kdsparks/data-efficient-satellite/gps/Example3_GetPosition/Example3_GetPosition.ino

/*
  Reading lat and long via UBX binary commands - no more NMEA parsing!
  By: Nathan Seidle
  SparkFun Electronics
  Date: January 3rd, 2019
  License: MIT. See license file for more information but you can
  basically do whatever you want with this code.

  This example shows how to query a u-blox module for its lat/long/altitude. We also
  turn off the NMEA output on the I2C port. This decreases the amount of I2C traffic 
  dramatically.

  Note: Long/lat are large numbers because they are * 10^7. To convert lat/long
  to something google maps understands simply divide the numbers by 10,000,000. We 
  do this so that we don't have to use floating point numbers.

  Leave NMEA parsing behind. Now you can simply ask the module for the datums you want!

  Feel like supporting open source hardware?
  Buy a board from SparkFun!
  ZED-F9P RTK2: https://www.sparkfun.com/products/15136
  NEO-M8P RTK: https://www.sparkfun.com/products/15005
  SAM-M8Q: https://www.sparkfun.com/products/15106

  Hardware Connections:
  Plug a Qwiic cable into the GNSS and a BlackBoard
  If you don't have a platform with a Qwiic connection use the SparkFun Qwiic Breadboard Jumper (https://www.sparkfun.com/products/14425)
  Open the serial monitor at 115200 baud to see the output
*/

#include <Wire.h> //Needed for I2C to GNSS

#include <SparkFun_u-blox_GNSS_Arduino_Library.h> //http://librarymanager/All#SparkFun_u-blox_GNSS
SFE_UBLOX_GNSS myGNSS;

long lastTime = 0; //Simple local timer. Limits amount if I2C traffic to u-blox module.

void setup()
{
  Serial.begin(115200);
  while (!Serial); //Wait for user to open terminal
  Serial.println("SparkFun u-blox Example");

  Wire1.begin();

  //myGNSS.enableDebugging(); // Uncomment this line to enable helpful debug messages on Serial

  if (myGNSS.begin(Wire1) == false) //Connect to the u-blox module using Wire port
  {
    Serial.println(F("u-blox GNSS not detected at default I2C address. Please check wiring. Freezing."));
    while (1);
  }

  myGNSS.setI2COutput(COM_TYPE_UBX); //Set the I2C port to output UBX only (turn off NMEA noise)
  myGNSS.saveConfigSelective(VAL_CFG_SUBSEC_IOPORT); //Save (only) the communications port settings to flash and BBR
}

void loop()
{
  //Query module only every second. Doing it more often will just cause I2C traffic.
  //The module only responds when a new position is available
  if (millis() - lastTime > 1000)
  {
    lastTime = millis(); //Update the timer
    
    long latitude = myGNSS.getLatitude(); // latitude gives raw GPS reading (degrees *10^-7)
    double actualLatitude = (double)latitude / 10000000.0; // divide by 10,000,000 to get lat readable by google maps
    Serial.print(F("Lat: "));
    Serial.print(actualLatitude, 6); // forces display of 6 decimals (or more)

    long longitude = myGNSS.getLongitude(); // longitude gives raw GPS reading (degrees *10^-7)
    double actualLongitude = (double)longitude / 10000000.0; // divide by 10,000,000 to get long readable by google maps
    Serial.print(F(" Long: "));
    Serial.print(actualLongitude, 6); // forces display of 6 decimals (or more)
    // Serial.print(F(" (degrees * 10^-7)")); this line isn't needed anymore

    long altitude = myGNSS.getAltitudeMSL(); // changed from getAltitude() to getAltitudeMSL()
    Serial.print(F(" Alt: "));
    Serial.print(altitude);
    Serial.print(F(" (mm)"));

    byte SIV = myGNSS.getSIV();
    Serial.print(F(" SIV: "));
    Serial.print(SIV);

    Serial.println();
  }
}
